jtsiomb/pss20midi/fw/src/midi.h

#ifndef MIDI_H_
#define MIDI_H_

#define MIDI_CMD_NOTEON 0x90
#define MIDI_CMD_NOTEOFF 0x80
#define MIDI_CMD_CHANMSG 0xb0
#define MIDI_CHANMSG_NOTES_OFF 0x7b

void midi_init(void);
void midi_all_off(void);
void midi_note(int chan, int note, int vel);

#endif /* MIDI_H_ */
